Ahnaf-nub/GeoPanel-Panel-for-Geo-Flight-Simulator/B612_Regular5pt7b.h

const uint8_t B612_Regular5pt7bBitmaps[] PROGMEM = {
  0x00, 0xF9, 0xF0, 0x12, 0x12, 0x7F, 0xA2, 0x24, 0xFF, 0x24, 0x24, 0x46,
  0xDC, 0xC7, 0x55, 0xE4, 0x62, 0x4A, 0x25, 0x0D, 0x00, 0xB0, 0xA4, 0x52,
  0x46, 0x21, 0x48, 0x10, 0xA6, 0xE9, 0x9F, 0xE0, 0xEA, 0xAA, 0xB0, 0xC9,
  0xB6, 0xDB, 0x58, 0x5E, 0x80, 0x21, 0x3E, 0x42, 0x00, 0xE0, 0xE0, 0x70,
  0x08, 0x84, 0x22, 0x11, 0x08, 0xC0, 0x74, 0xA3, 0x18, 0xC5, 0x2E, 0x26,
  0xA2, 0x22, 0x27, 0xE9, 0x13, 0x24, 0x8F, 0xF2, 0x26, 0x11, 0x3C, 0x44,
  0x48, 0xAA, 0xF2, 0xF8, 0x8E, 0x11, 0x2C, 0x32, 0x21, 0xF8, 0xC6, 0x2E,
  0xF8, 0x84, 0x42, 0x21, 0x08, 0x74, 0xE4, 0xC9, 0xC6, 0x2E, 0x74, 0x63,
  0x17, 0x8C, 0x4C, 0xD0, 0xDC, 0x1B, 0x21, 0x83, 0x04, 0xF8, 0x3E, 0x83,
  0x06, 0x6C, 0x40, 0x69, 0x13, 0x64, 0x04, 0x18, 0x66, 0xDB, 0xA5, 0x9D,
  0xA5, 0xA5, 0xBF, 0x40, 0x3C, 0x23, 0x14, 0xA5, 0x7E, 0x31, 0xE9, 0x9E,
  0x99, 0x9E, 0x7A, 0x21, 0x08, 0x41, 0x0F, 0xF4, 0xA3, 0x18, 0xC6, 0x5C,
  0xF8, 0x8E, 0x88, 0x8F, 0xF8, 0x8E, 0x88, 0x88, 0x79, 0x08, 0x27, 0x86,
  0x14, 0x4E, 0x8C, 0x63, 0xF8, 0xC6, 0x31, 0xFF, 0x64, 0x92, 0x4E, 0x8C,
  0xA9, 0x8E, 0x52, 0x53, 0x88, 0x88, 0x88, 0x8F, 0x83, 0x8F, 0x1F, 0x5A,
  0xB5, 0x64, 0xC1, 0x87, 0x1E, 0x69, 0x96, 0x58, 0xE1, 0x79, 0x28, 0x61,
  0x86, 0x14, 0x9E, 0xF4, 0x63, 0x1F, 0x42, 0x10, 0x31, 0x28, 0x61, 0x86,
  0x1B, 0x5E, 0x04, 0xF4, 0x63, 0x1F, 0x52, 0x51, 0x78, 0x86, 0x31, 0x1E,
  0xF9, 0x08, 0x42, 0x10, 0x84, 0x8C, 0x63, 0x18, 0xC6, 0x2E, 0xC6, 0x89,
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
  {   148,   4,   8,   6,    1,   -7 },   // 0x46 'F'
  {   152,   6,   8,   7,    0,   -7 },   // 0x47 'G'
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

const GFXfont B612_Regular5pt7b PROGMEM = {
  (uint8_t  *)B612_Regular5pt7bBitmaps,
  (GFXglyph *)B612_Regular5pt7bGlyphs,
  0x20, 0x7E, 12 };

// Approx. 1069 bytes
